tbriggs6/railroad/source/handlers.h

/* 
 * File:   handlers.h
 * Author: tbriggs
 *
 * Created on July 24, 2019, 9:47 AM
 */

#ifndef HANDLERS_H
#define	HANDLERS_H

#ifdef	__cplusplus
extern "C" {
#endif


    void handle_adc( );
    void handle_timer( );
    

#ifdef	__cplusplus
}
#endif

#endif	/* HANDLERS_H */
